TT-392/arisu-split/Case/kicad_export/cutouts.dxf

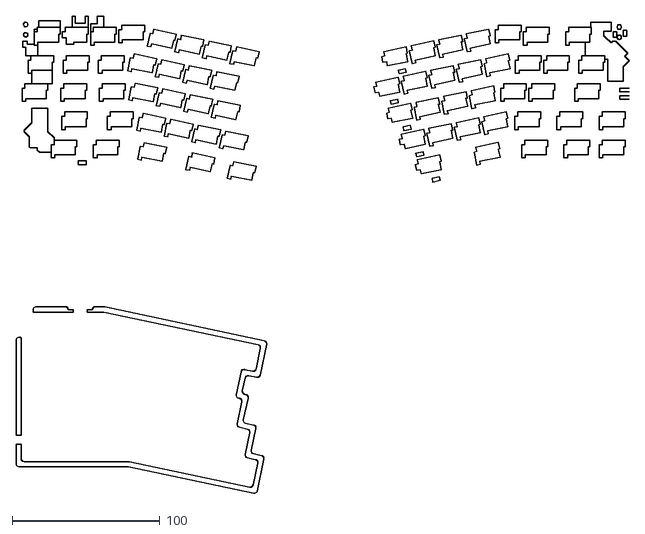
[picture p21: CAD file, 2022-11-08]
Case/kicad_export/cutouts.dxf
414.5 x 322.7
