TT-392/arisu-split/3d models/cherry-mx-keycaps/STL/1x1.5 R4.stl

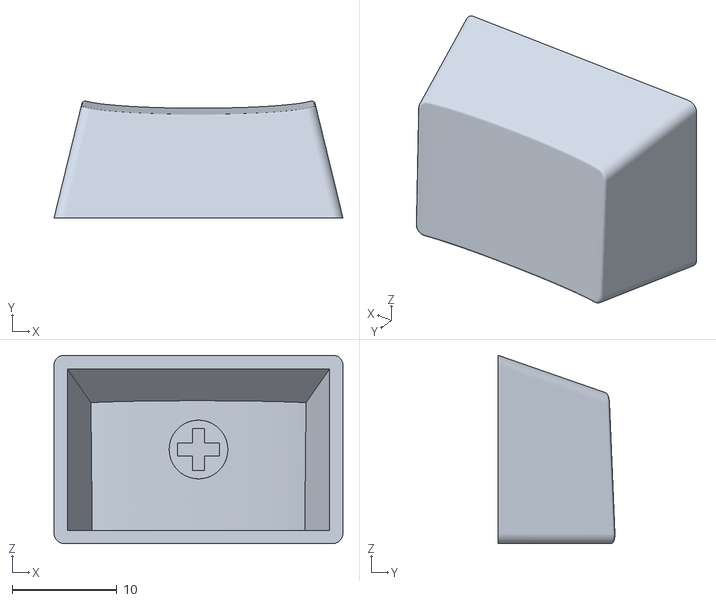
[picture p22: CAD file, 2022-08-18]
3d models/cherry-mx-keycaps/STL/1x1.5 R4.stl
27.6 x 11.2 x 18.0
