TT-392/arisu-split/Case/kicad_export/bottom.dxf

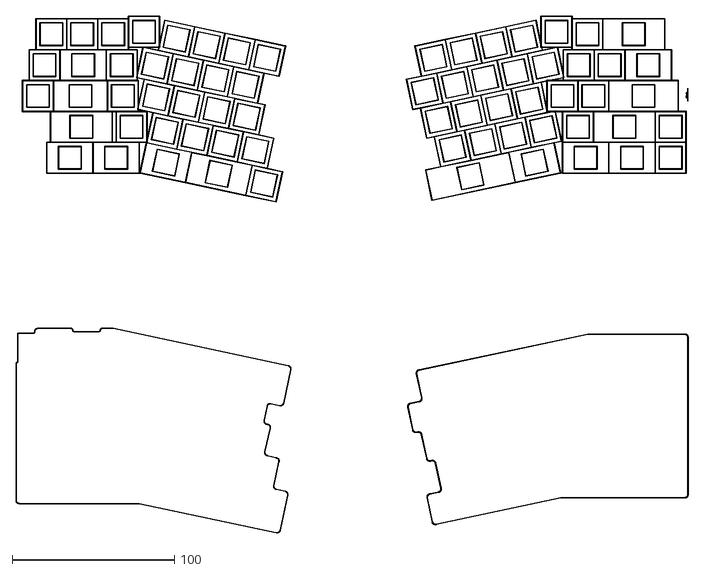
[picture p23: CAD file, 2022-11-08]
Case/kicad_export/bottom.dxf
414.6 x 318.7
