TT-392/arisu-split/3d models/cherry-mx-keycaps/STL/1x1.25 R4.stl

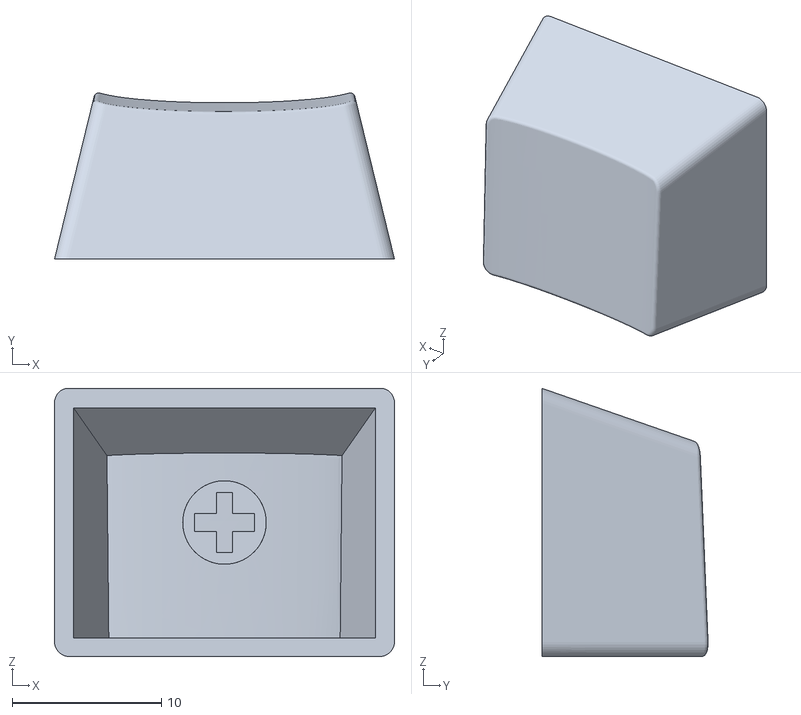
[picture p25: CAD file, 2022-08-18]
3d models/cherry-mx-keycaps/STL/1x1.25 R4.stl
22.8 x 11.1 x 18.0
