TT-392/arisu-split/3d models/cherry-mx-keycaps/STL/1x2.25 R2.stl

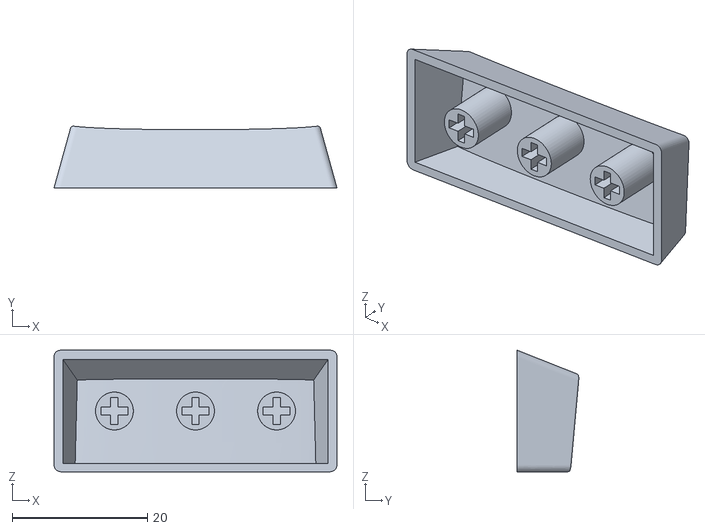
[picture p26: CAD file, 2022-08-18]
3d models/cherry-mx-keycaps/STL/1x2.25 R2.stl
41.9 x 9.12 x 18.0
