TT-392/arisu-split/3d models/cherry-mx-keycaps/STL/1x1.5 R3.stl

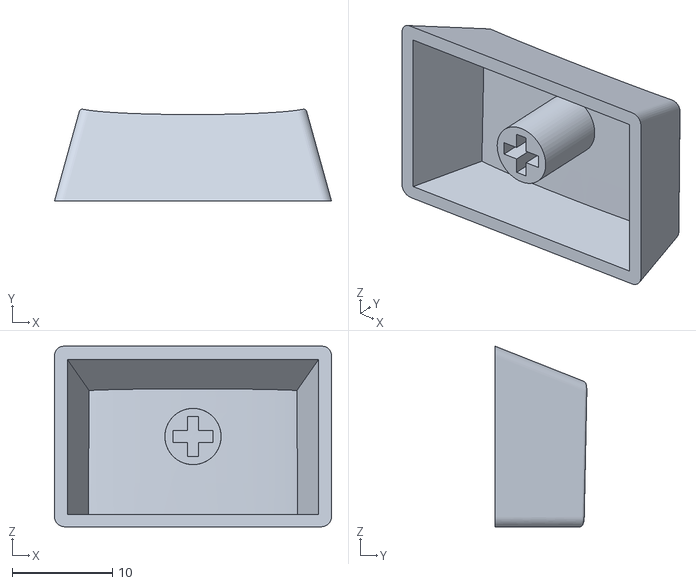
[picture p31: CAD file, 2022-08-18]
3d models/cherry-mx-keycaps/STL/1x1.5 R3.stl
27.6 x 9.14 x 18.0
