TT-392/arisu-split/3d models/cherry-mx-keycaps/STL/1x1.75 R1.stl

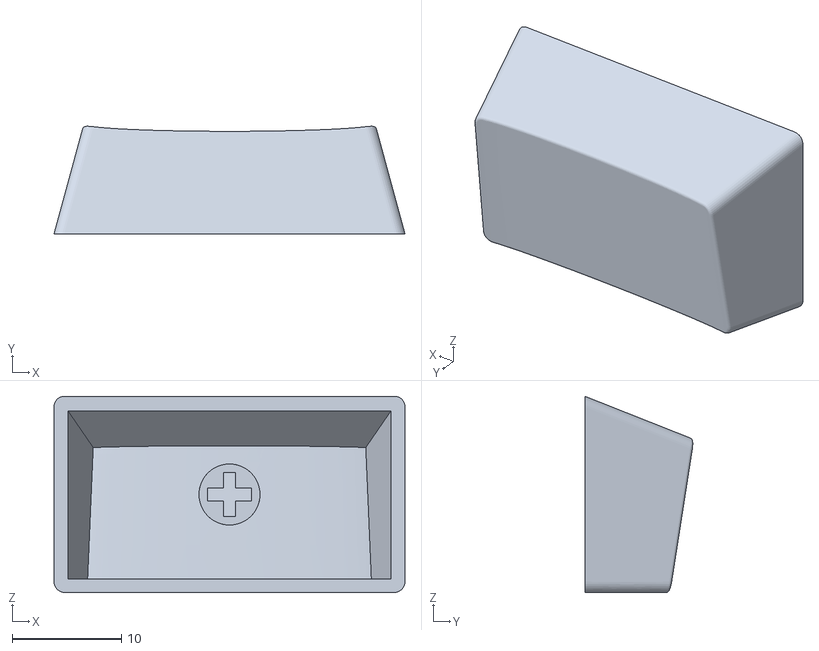
[picture p32: CAD file, 2022-08-18]
3d models/cherry-mx-keycaps/STL/1x1.75 R1.stl
32.2 x 9.87 x 18.0
