TT-392/arisu-split/3d models/cherry-mx-keycaps/STL/1x6.25 R3.stl

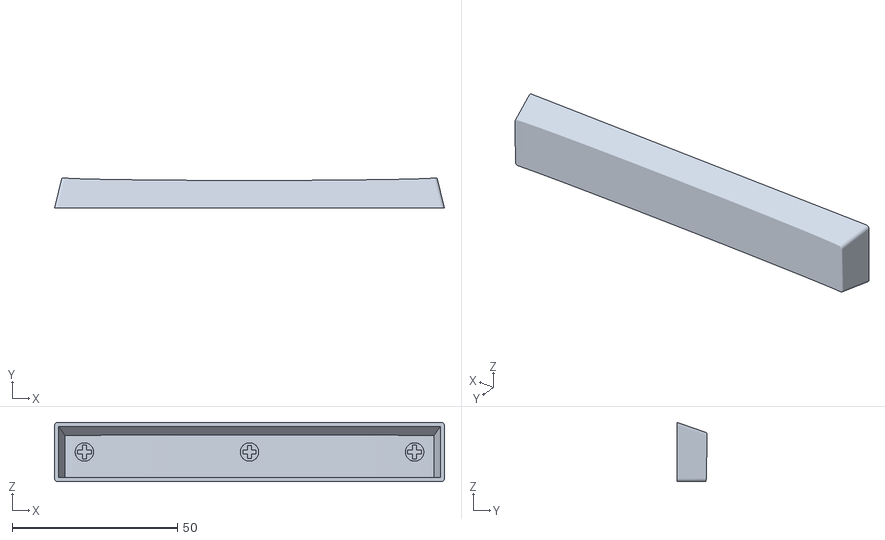
[picture p34: CAD file, 2022-08-18]
3d models/cherry-mx-keycaps/STL/1x6.25 R3.stl
118.1 x 9.20 x 18.0
