TT-392/arisu-split/3d models/cherry-mx-keycaps/STL/1x1.75 R2.stl

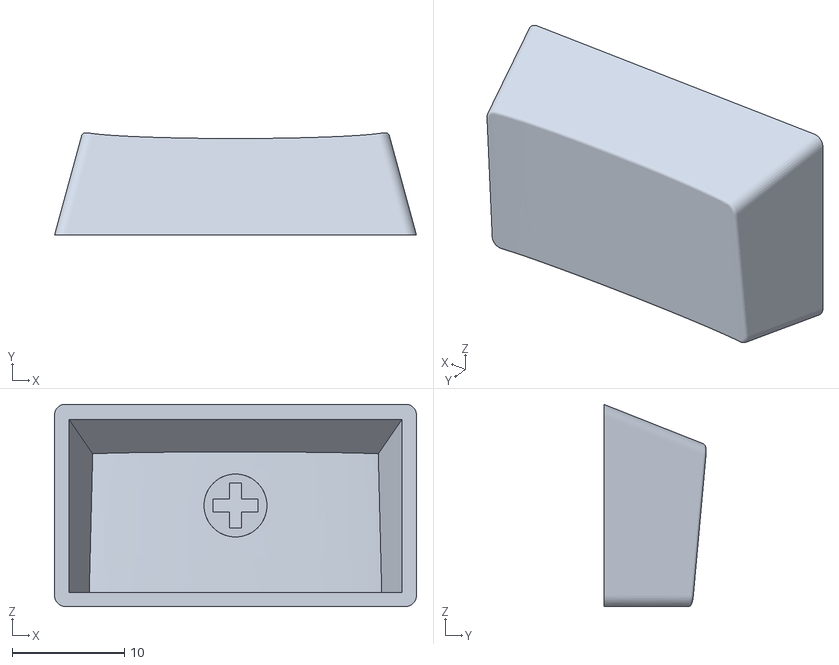
[picture p35: CAD file, 2022-08-18]
3d models/cherry-mx-keycaps/STL/1x1.75 R2.stl
32.2 x 9.10 x 18.0
