TT-392/arisu-split/3d models/cherry-mx-keycaps/STL/1x2.25 R1.stl

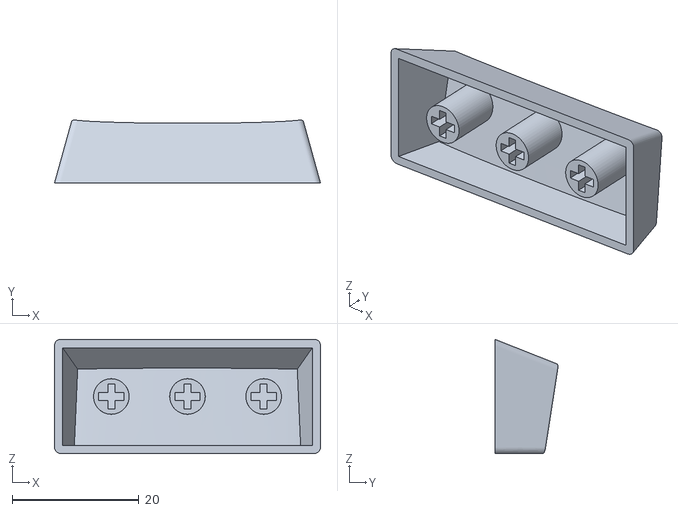
[picture p36: CAD file, 2022-08-18]
3d models/cherry-mx-keycaps/STL/1x2.25 R1.stl
41.9 x 9.89 x 18.0
