TT-392/arisu-split/3d models/cherry-mx-keycaps/STL/1x2.75 R3.stl

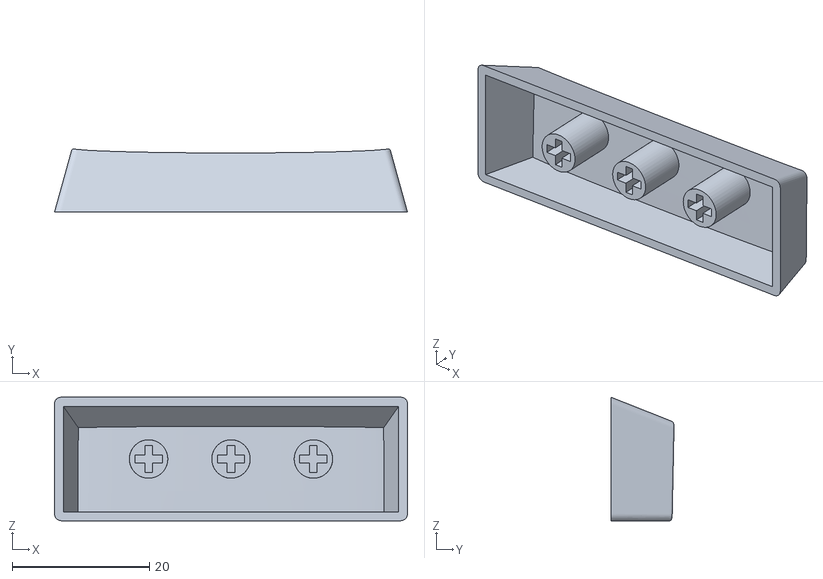
[picture p37: CAD file, 2022-08-18]
3d models/cherry-mx-keycaps/STL/1x2.75 R3.stl
51.4 x 9.18 x 18.0
