TT-392/arisu-split/3d models/cherry-mx-keycaps/STL/1x2 R2.stl

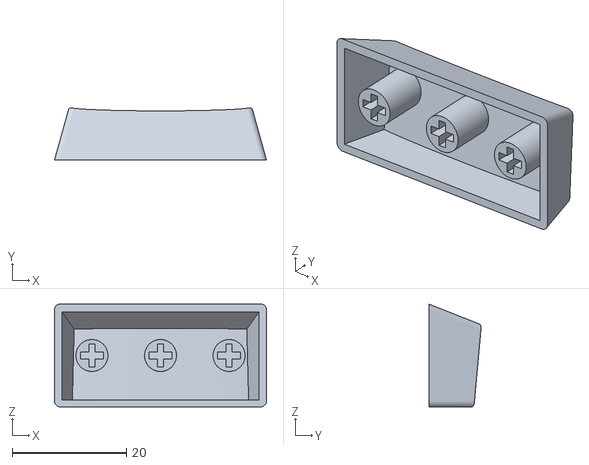
[picture p39: CAD file, 2022-08-18]
3d models/cherry-mx-keycaps/STL/1x2 R2.stl
37.1 x 9.12 x 18.0
