TT-392/arisu-split/3d models/cherry-mx-keycaps/STL/1x2.5 R2.stl

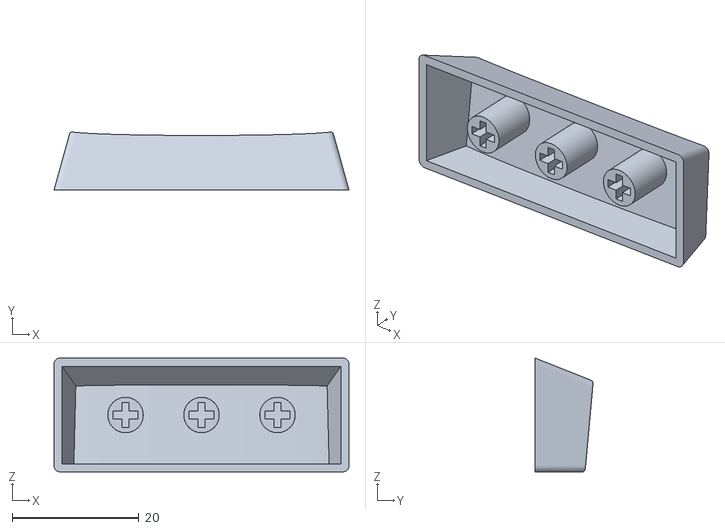
[picture p40: CAD file, 2022-08-18]
3d models/cherry-mx-keycaps/STL/1x2.5 R2.stl
46.6 x 9.13 x 18.0
