TT-392/arisu-split/3d models/cherry-mx-keycaps/STL/1x1.25 R1.stl

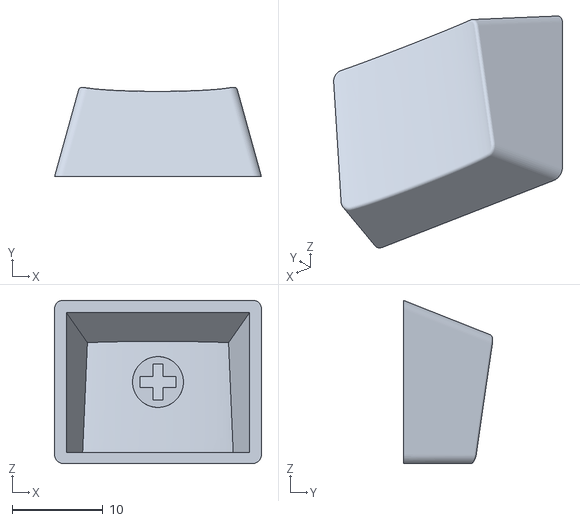
[picture p41: CAD file, 2022-08-18]
3d models/cherry-mx-keycaps/STL/1x1.25 R1.stl
22.8 x 9.84 x 18.0
