TT-392/arisu-split/3d models/cherry-mx-keycaps/STL/1x1.5 R1.stl

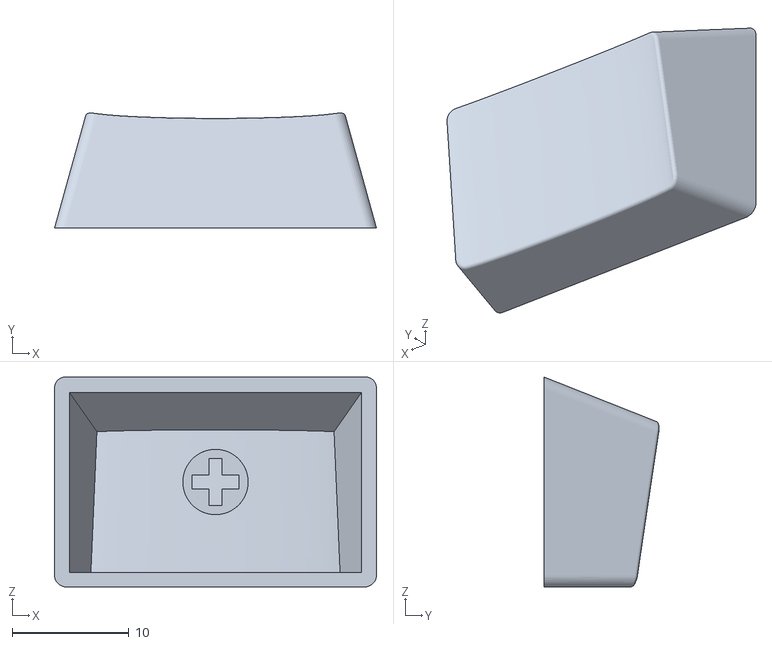
[picture p43: CAD file, 2022-08-18]
3d models/cherry-mx-keycaps/STL/1x1.5 R1.stl
27.6 x 9.86 x 18.0
