TT-392/arisu-split/3d models/cherry-mx-keycaps/STL/1x1 R2.stl

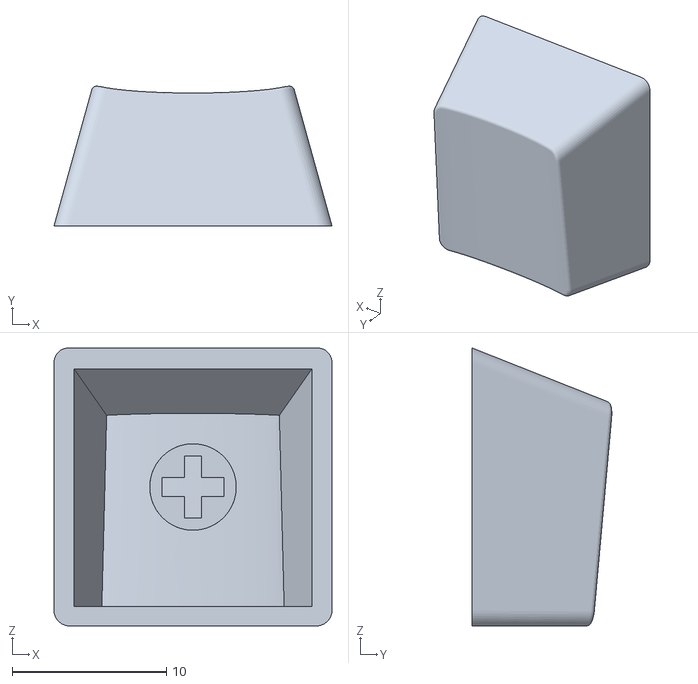
[picture p44: CAD file, 2022-08-18]
3d models/cherry-mx-keycaps/STL/1x1 R2.stl
18.0 x 9.04 x 18.0
