TT-392/arisu-split/3d models/cherry-mx-keycaps/STL/1x2.25 R4.stl

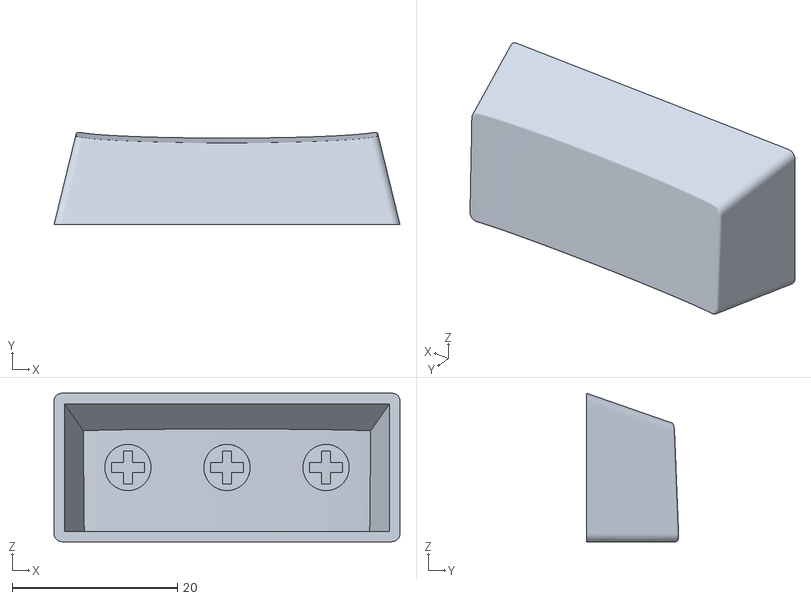
[picture p46: CAD file, 2022-08-18]
3d models/cherry-mx-keycaps/STL/1x2.25 R4.stl
41.9 x 11.2 x 18.0
