TT-392/arisu-split/3d models/cherry-mx-keycaps/STL/1x2.75 R4.stl

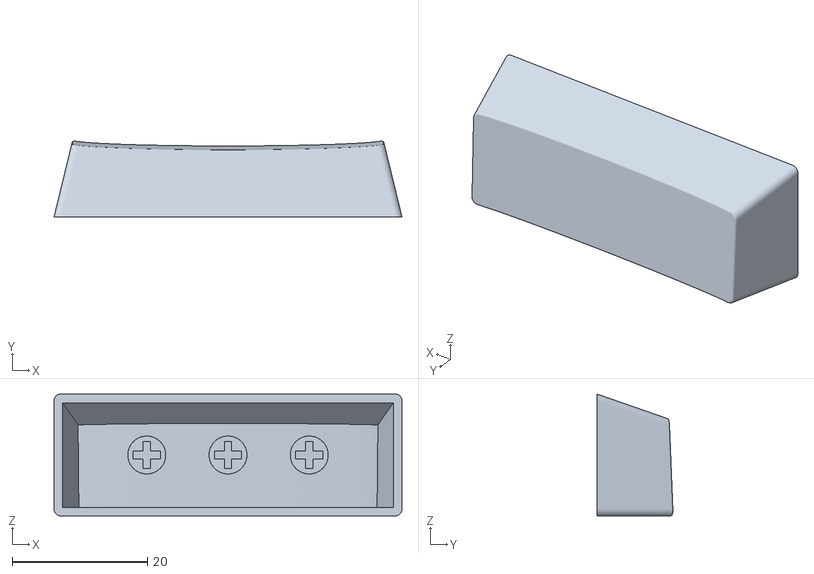
[picture p47: CAD file, 2022-08-18]
3d models/cherry-mx-keycaps/STL/1x2.75 R4.stl
51.4 x 11.2 x 18.0
