TT-392/arisu-split/3d models/cherry-mx-keycaps/STL/1x2.75 R2.stl

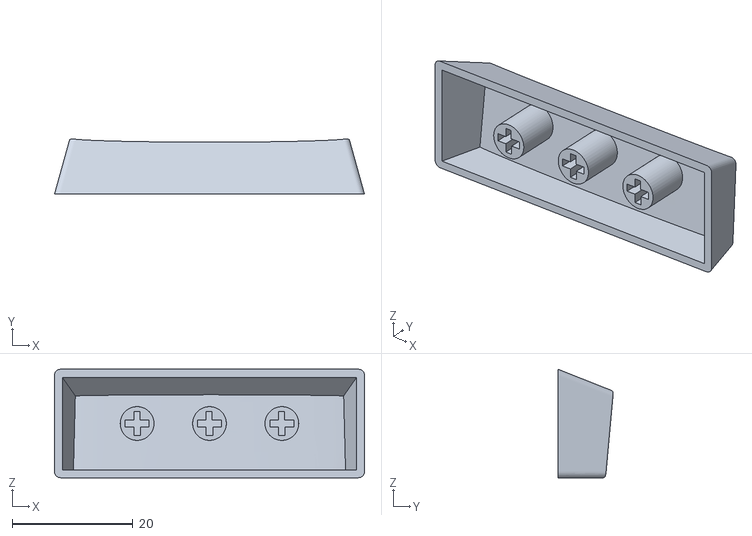
[picture p48: CAD file, 2022-08-18]
3d models/cherry-mx-keycaps/STL/1x2.75 R2.stl
51.4 x 9.14 x 18.0
