TT-392/arisu-split/3d models/cherry-mx-keycaps/STL/1x2 R1.stl

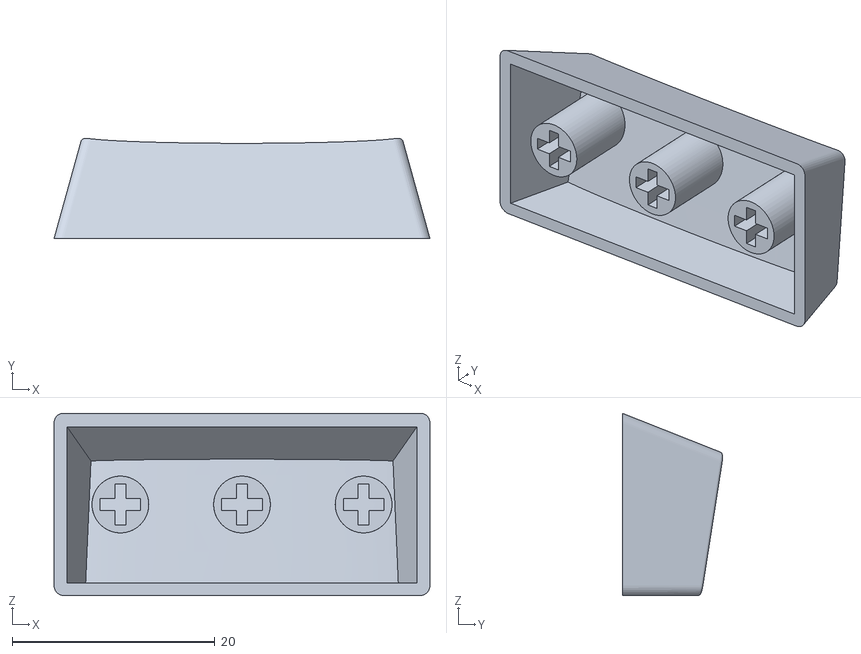
[picture p49: CAD file, 2022-08-18]
3d models/cherry-mx-keycaps/STL/1x2 R1.stl
37.1 x 9.88 x 18.0
