TT-392/arisu-split/3d models/cherry-mx-keycaps/STL/1x2.25 R3.stl

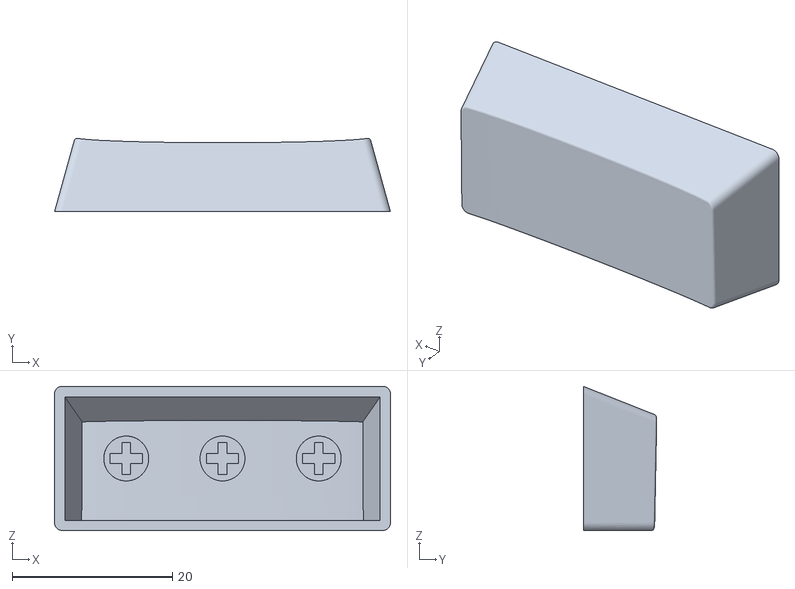
[picture p50: CAD file, 2022-08-18]
3d models/cherry-mx-keycaps/STL/1x2.25 R3.stl
41.9 x 9.16 x 18.0
