TT-392/arisu-split/3d models/cherry-mx-keycaps/STL/1x1.75 R4.stl

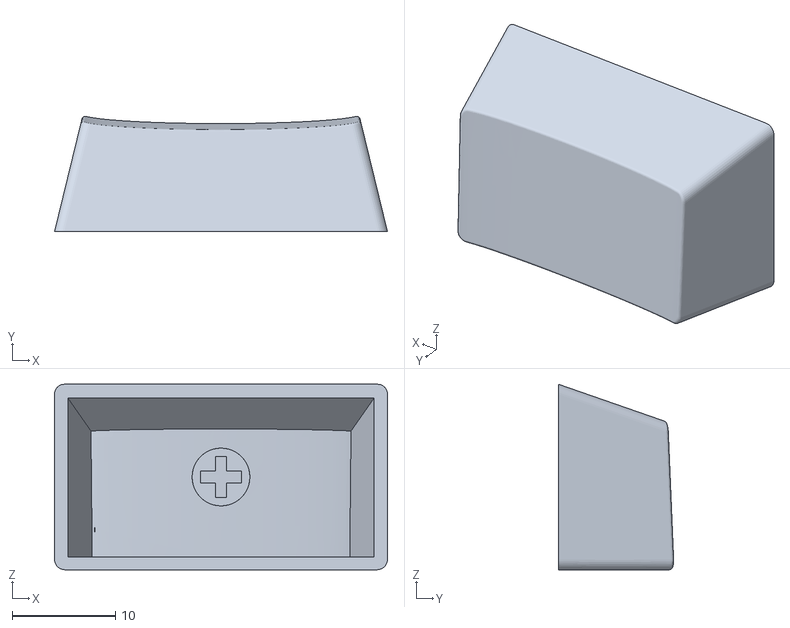
[picture p51: CAD file, 2022-08-18]
3d models/cherry-mx-keycaps/STL/1x1.75 R4.stl
32.3 x 11.2 x 18.0
