TT-392/arisu-split/3d models/cherry-mx-keycaps/STL/1x1 R4.stl

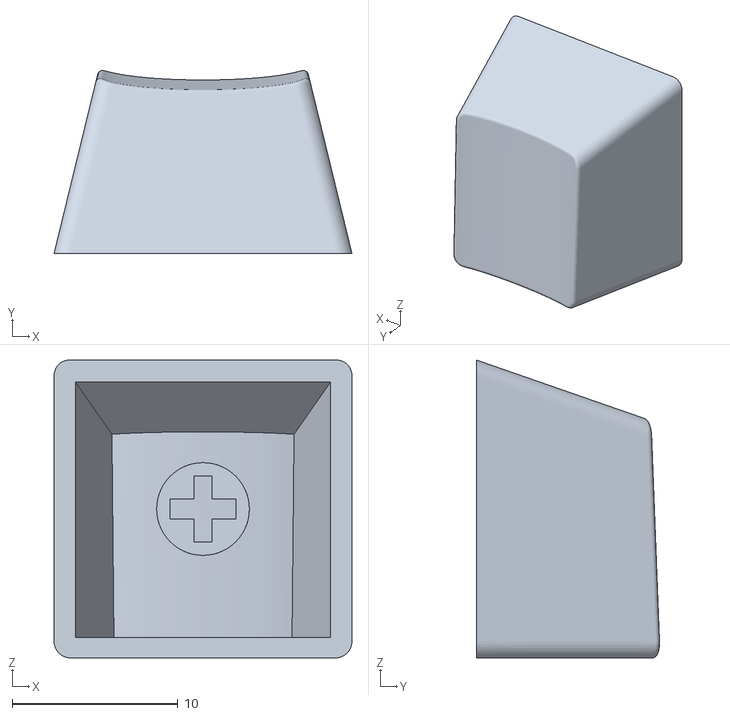
[picture p52: CAD file, 2022-08-18]
3d models/cherry-mx-keycaps/STL/1x1 R4.stl
18.0 x 11.1 x 18.0
