TT-392/arisu-split/3d models/cherry-mx-keycaps/STL/1x6.25 R4.stl

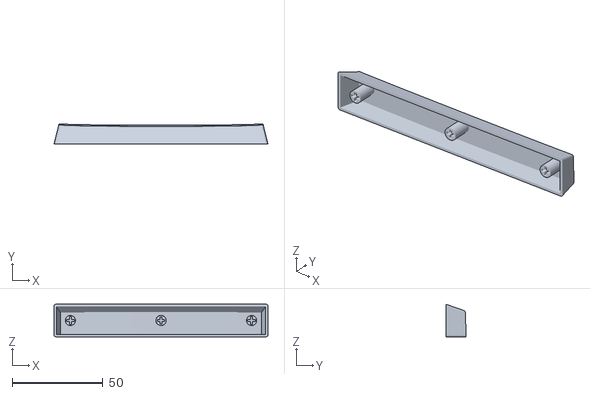
[picture p53: CAD file, 2022-08-18]
3d models/cherry-mx-keycaps/STL/1x6.25 R4.stl
118.1 x 11.3 x 18.0
